DingoOz/Work-Bot/Electrical Files/Teensy 2 digital pins.jpg

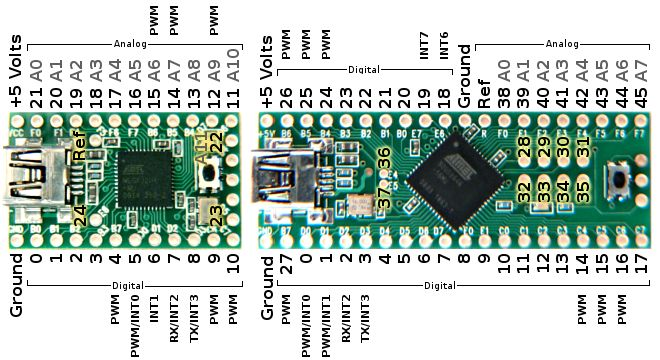
Electrical Files/Teensy 2 digital pins.jpg
