DingoOz/Work-Bot/Electrical Files/Main PCB Board.png

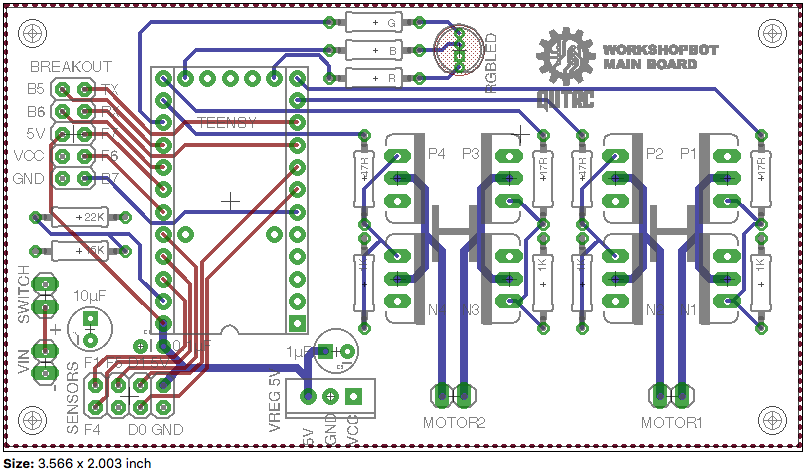
Electrical Files/Main PCB Board.png
